cemizm/AnySensePro/Dokumentation/Anschluesse.png

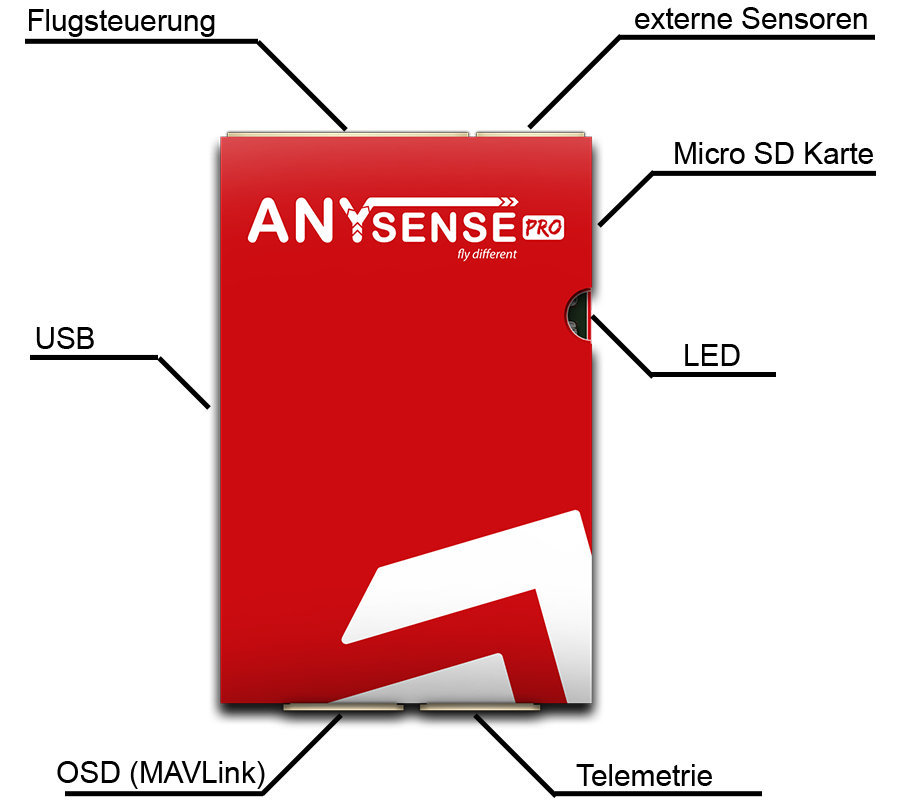
Dokumentation/Anschluesse.png
