cemizm/AnySensePro/Dokumentation/Aufkleber Be A Pro.png

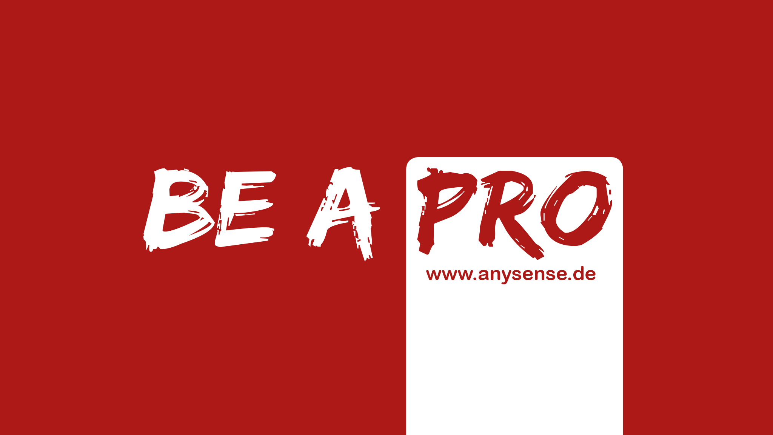
Dokumentation/Aufkleber Be A Pro.png
