cemizm/AnySensePro/Dokumentation/Fotos/AnySense Pro Detail 1.jpg

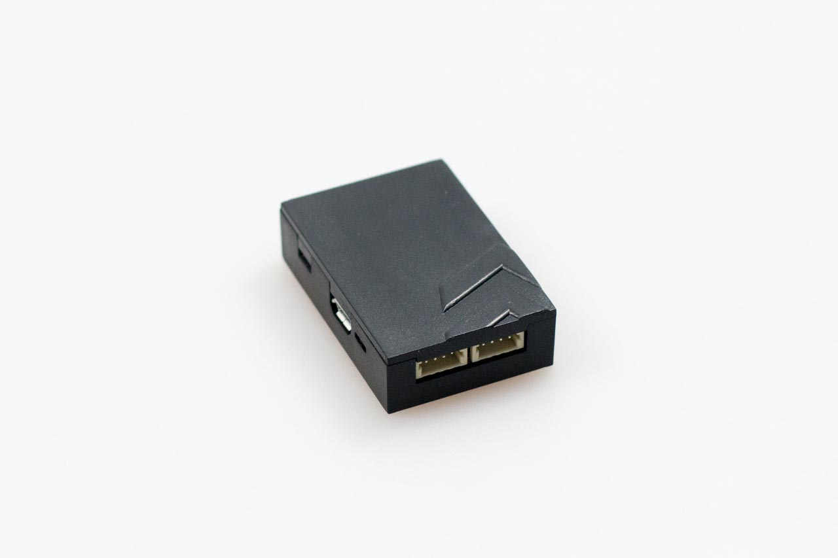
Dokumentation/Fotos/AnySense Pro Detail 1.jpg
