cemizm/AnySensePro/Dokumentation/Fotos/AnySense Pro Detail 2.jpg

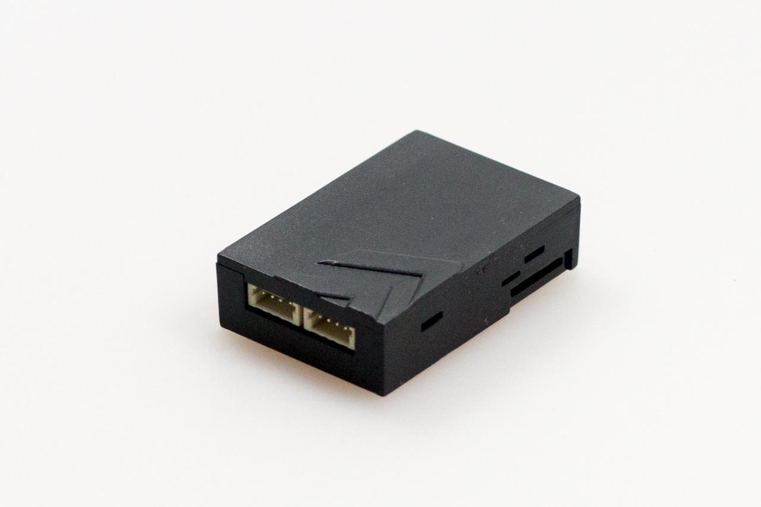
Dokumentation/Fotos/AnySense Pro Detail 2.jpg
