cemizm/AnySensePro/Dokumentation/Fotos/AnySense Pro Lieferumfang.jpg

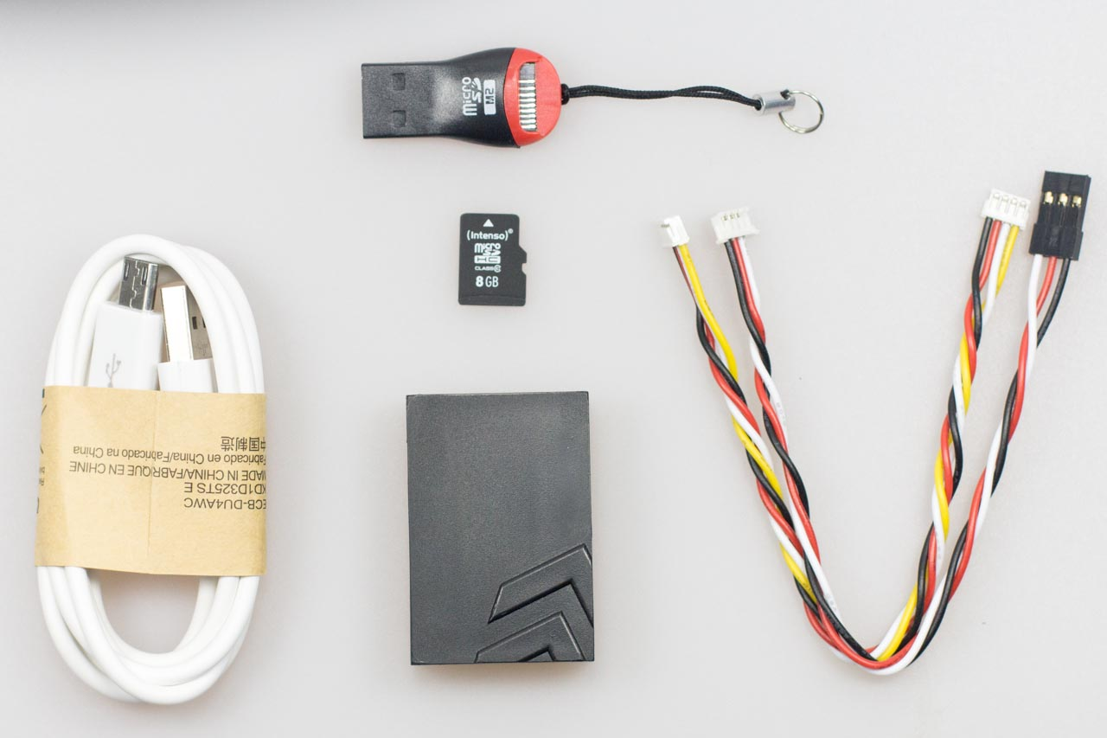
Dokumentation/Fotos/AnySense Pro Lieferumfang.jpg
