cemizm/AnySensePro/Dokumentation/Fotos/AnySense Pro Telemetrie Kabel.jpg

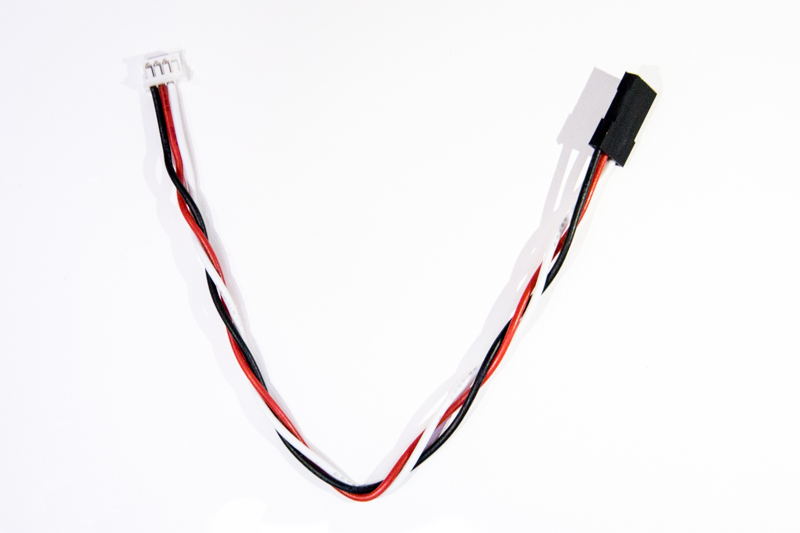
Dokumentation/Fotos/AnySense Pro Telemetrie Kabel.jpg
