cemizm/AnySensePro/Dokumentation/Fotos/AnySense Pro.jpg

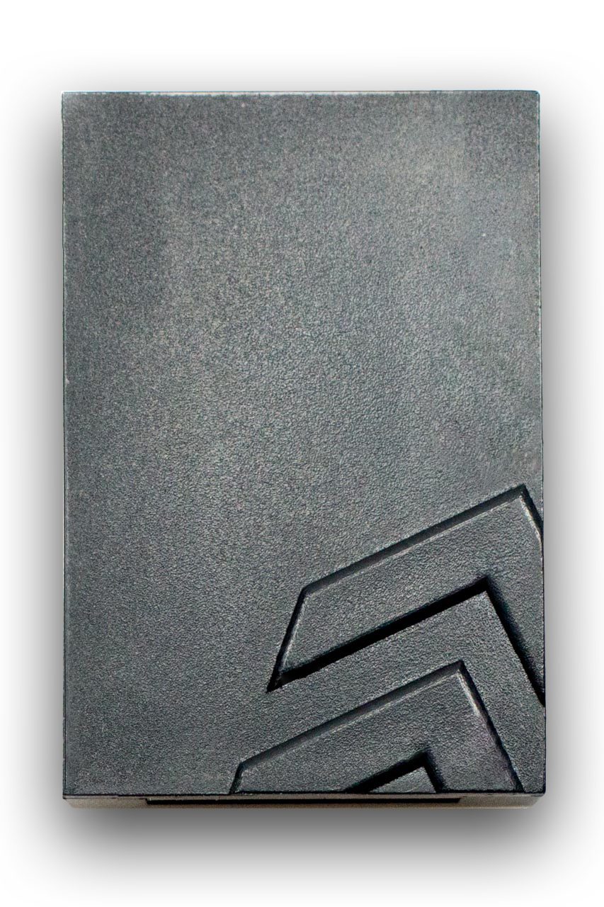
Dokumentation/Fotos/AnySense Pro.jpg
