cemizm/AnySensePro/Dokumentation/Fotos/AnySense Pro.png

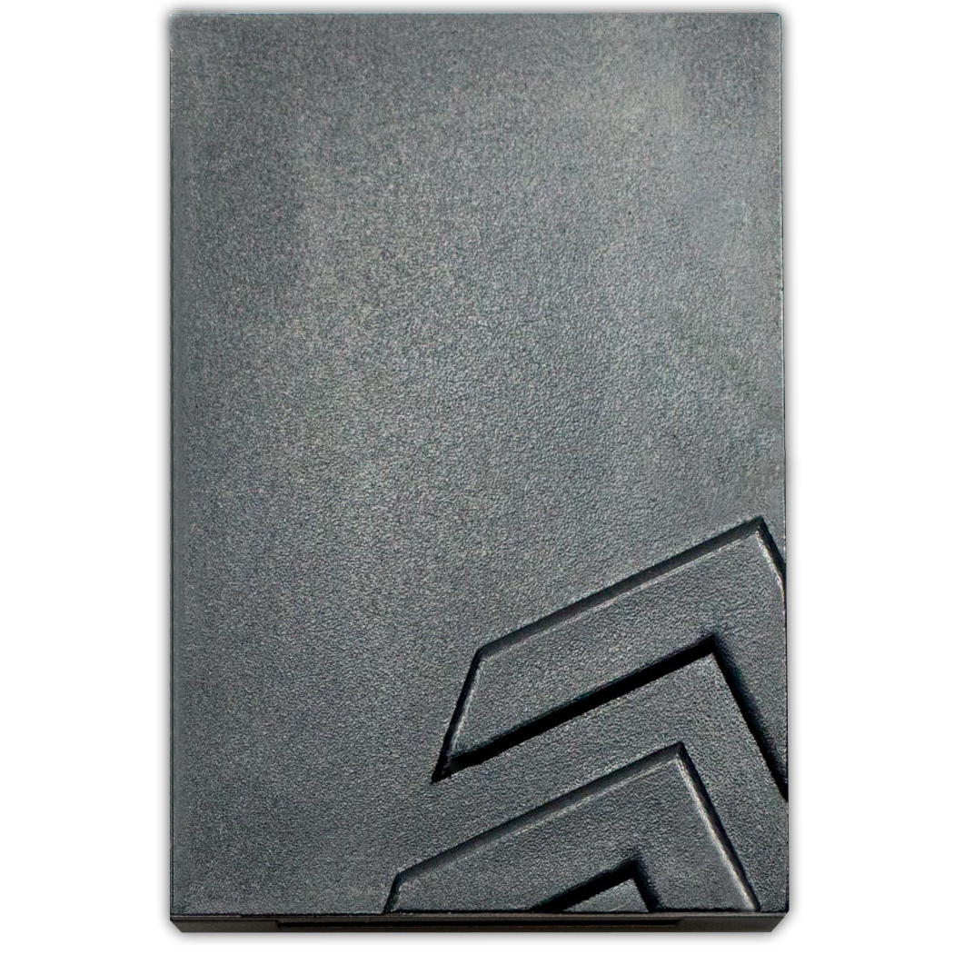
Dokumentation/Fotos/AnySense Pro.png
