cemizm/AnySensePro/Dokumentation/Fotos/Flugsteuerung Align.jpg

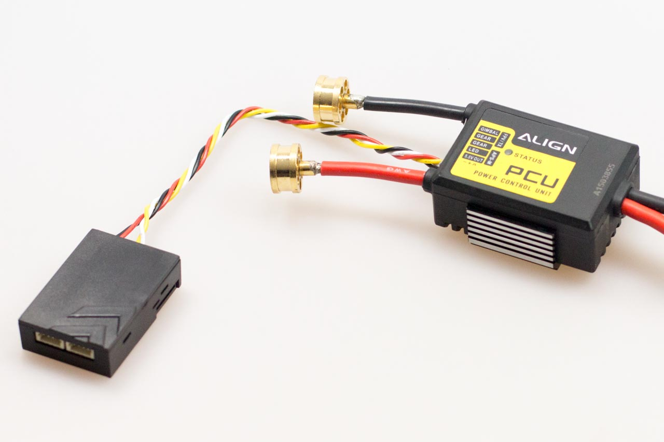
Dokumentation/Fotos/Flugsteuerung Align.jpg
