cemizm/AnySensePro/Dokumentation/Fotos/Flugsteuerung Naza.jpg

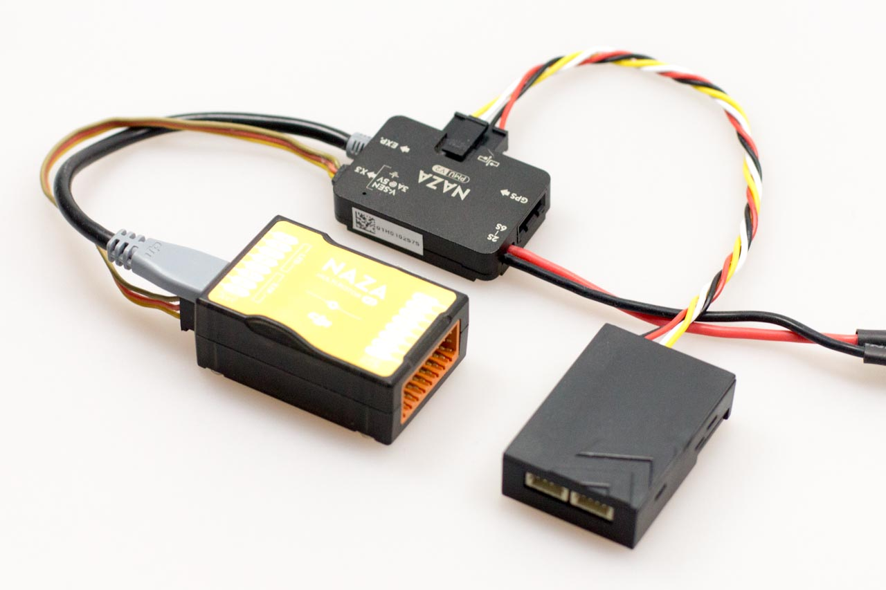
Dokumentation/Fotos/Flugsteuerung Naza.jpg
