cemizm/AnySensePro/Dokumentation/Fotos/Flugsteuerung Tarot.jpg

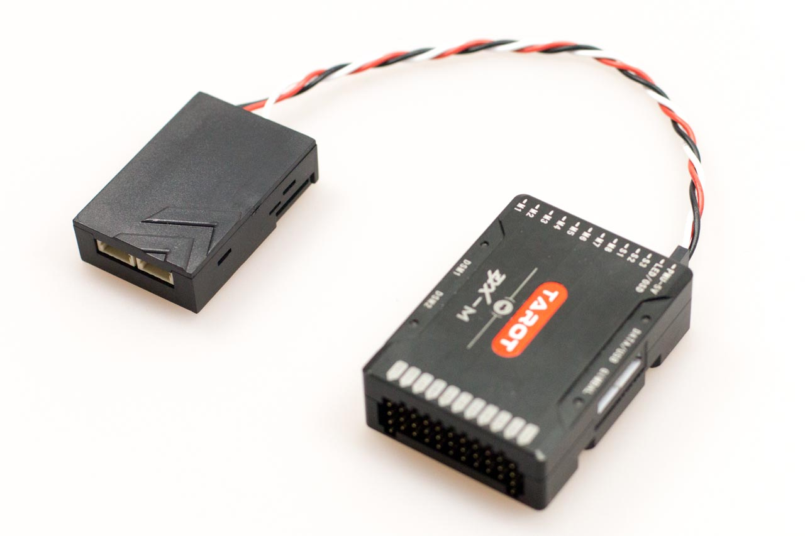
Dokumentation/Fotos/Flugsteuerung Tarot.jpg
