cemizm/AnySensePro/Dokumentation/Fotos/Kabel CANBus.jpg

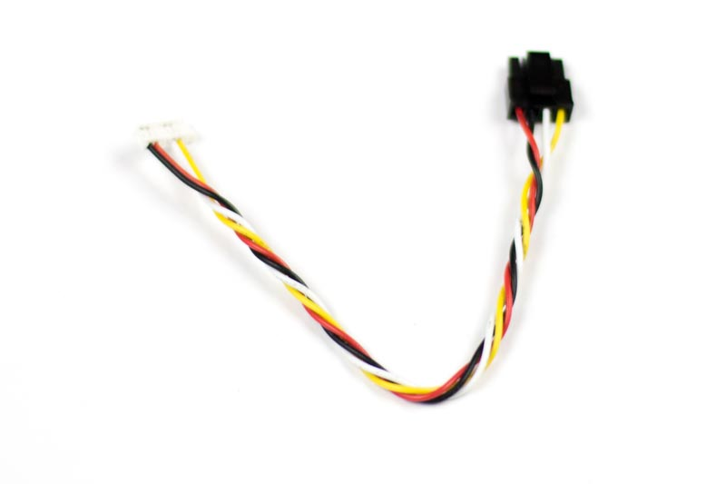
Dokumentation/Fotos/Kabel CANBus.jpg
