cemizm/AnySensePro/Dokumentation/Fotos/Kabel MAVLink.jpg

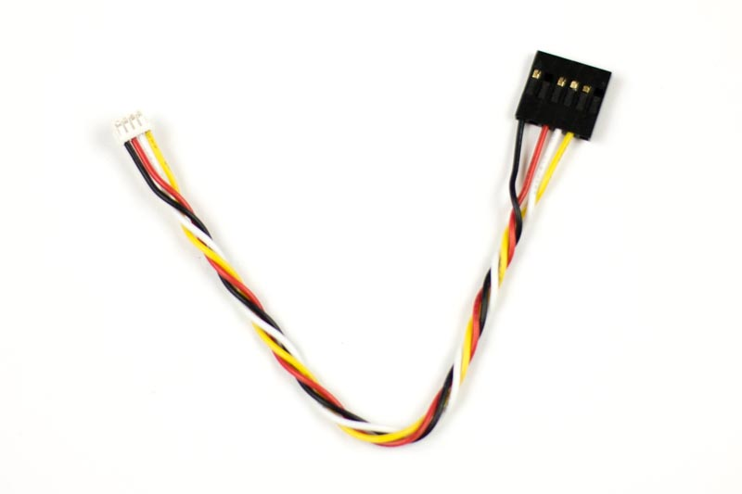
Dokumentation/Fotos/Kabel MAVLink.jpg
