cemizm/AnySensePro/Dokumentation/Fotos/Kabel PixHawk.jpg

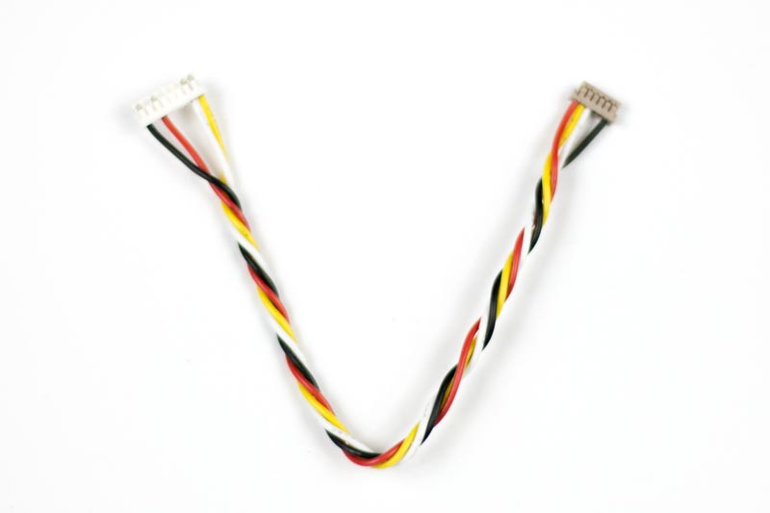
Dokumentation/Fotos/Kabel PixHawk.jpg
