cemizm/AnySensePro/Dokumentation/Fotos/Kabel Tarot.jpg

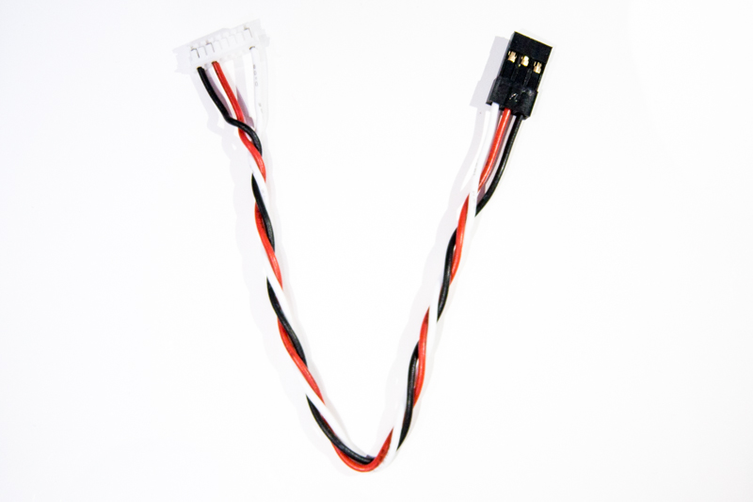
Dokumentation/Fotos/Kabel Tarot.jpg
