cemizm/AnySensePro/Dokumentation/Fotos/Telemetrie FrSky.jpg

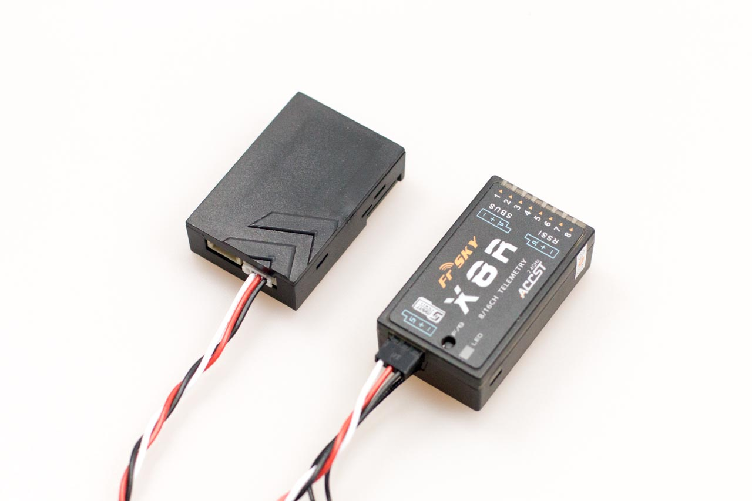
Dokumentation/Fotos/Telemetrie FrSky.jpg
