cemizm/AnySensePro/Dokumentation/Fotos/Telemetrie Futaba.jpg

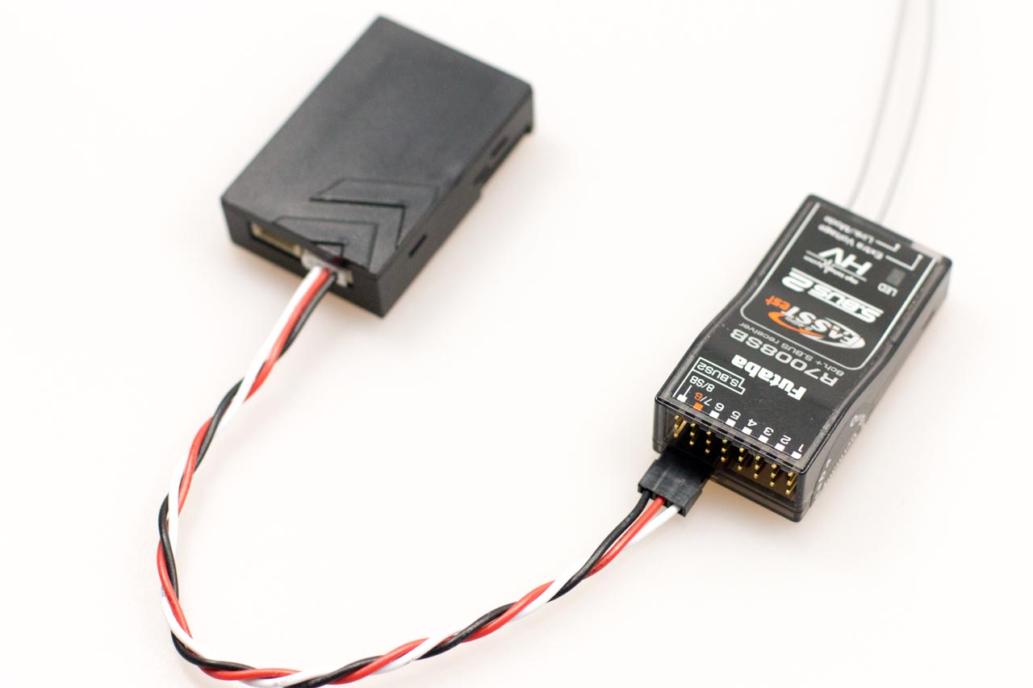
Dokumentation/Fotos/Telemetrie Futaba.jpg
