cemizm/AnySensePro/Dokumentation/Fotos/Telemetrie Graupner.jpg

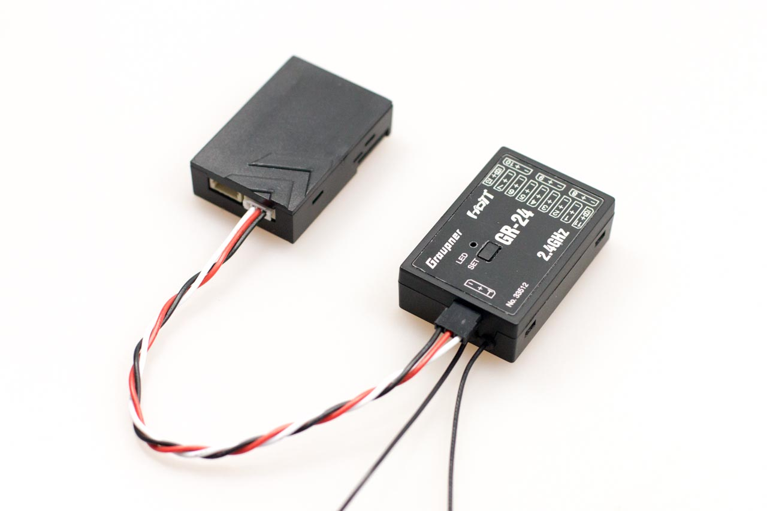
Dokumentation/Fotos/Telemetrie Graupner.jpg
