cemizm/AnySensePro/Dokumentation/Fotos/Telemetrie Jeti.jpg

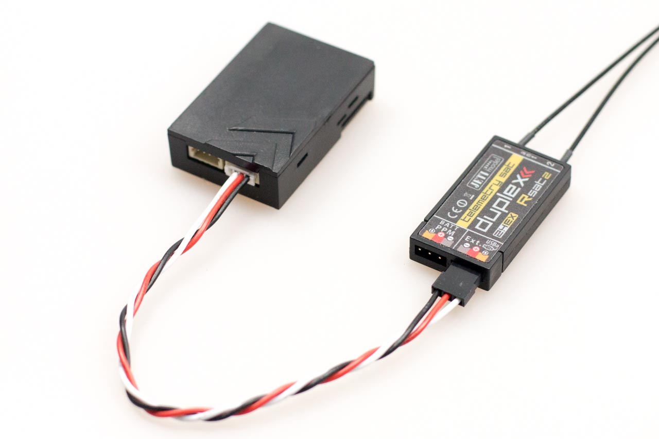
Dokumentation/Fotos/Telemetrie Jeti.jpg
