cemizm/AnySensePro/Dokumentation/Fotos/Telemetrie Multiplex.jpg

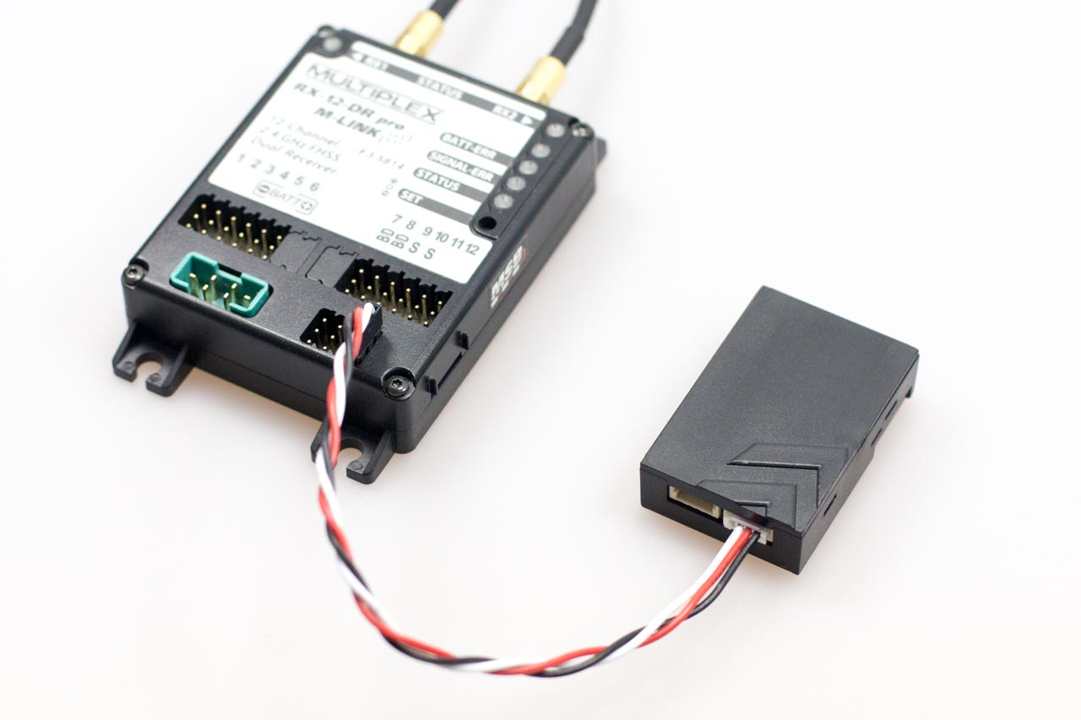
Dokumentation/Fotos/Telemetrie Multiplex.jpg
