cemizm/AnySensePro/Dokumentation/Fotos/Telemetrie Spektrum.jpg

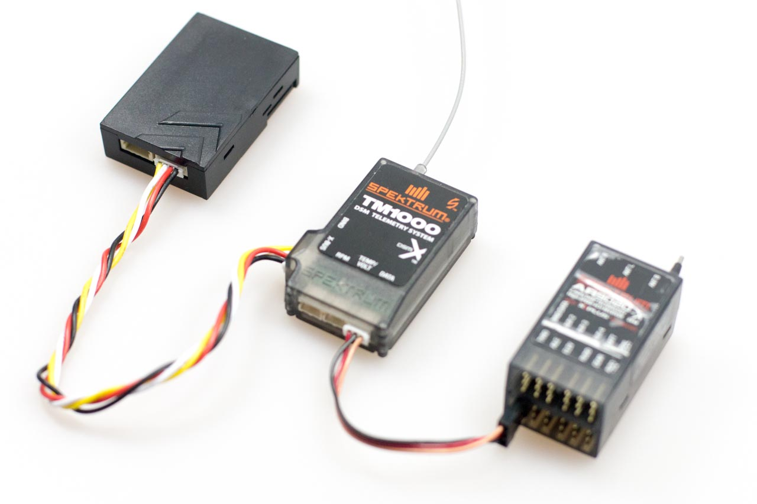
Dokumentation/Fotos/Telemetrie Spektrum.jpg
