cemizm/AnySensePro/Dokumentation/Futuba.JPG

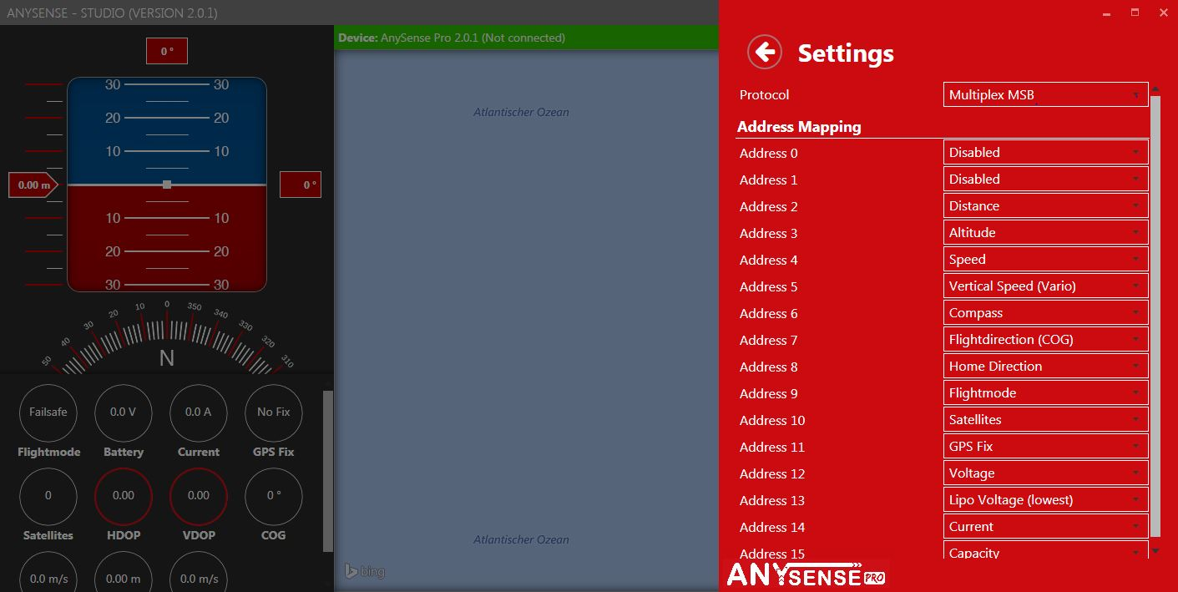
Dokumentation/Futuba.JPG
