cemizm/AnySensePro/Hardware/Kabel/CANBusKabel.pdf

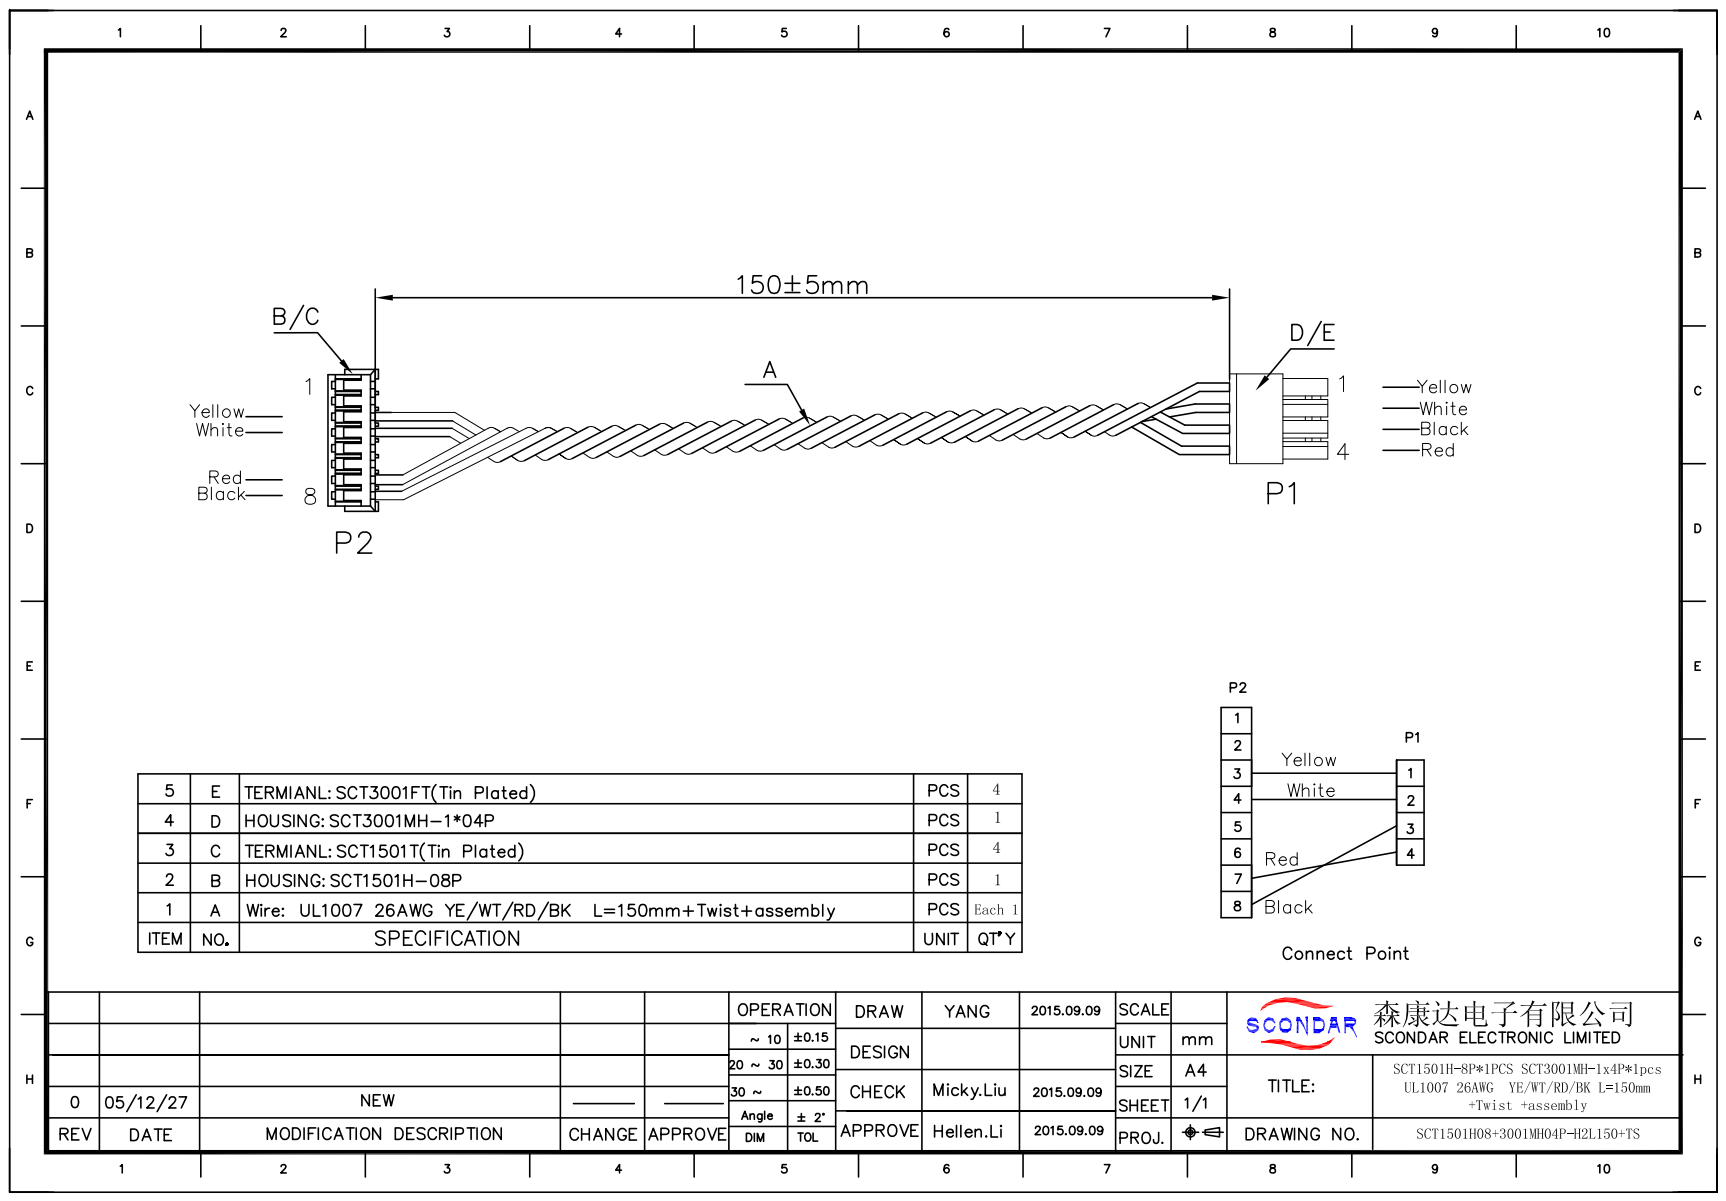
[picture p44: page 1]
