cemizm/AnySensePro/Hardware/Kabel/OSDKabel.pdf

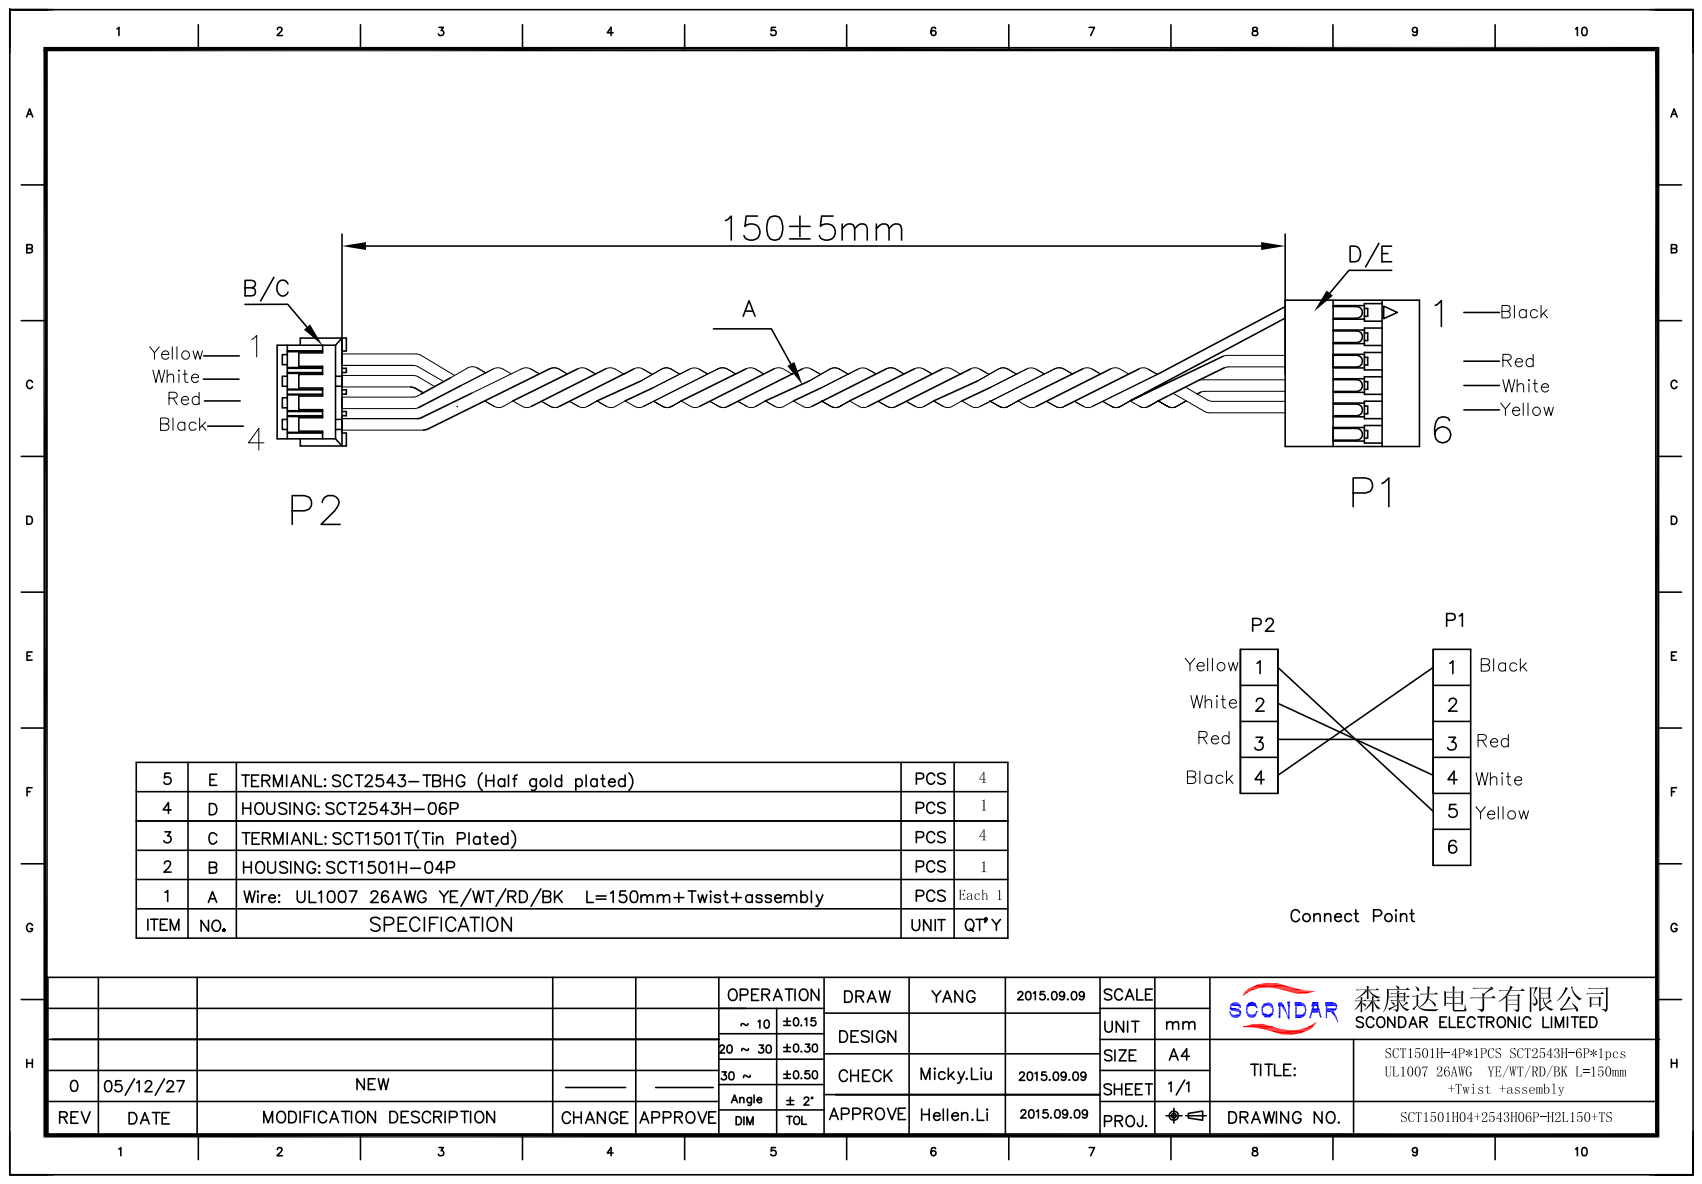
[picture p45: page 1]
