cemizm/AnySensePro/Hardware/Kabel/PixhawkKabel.pdf

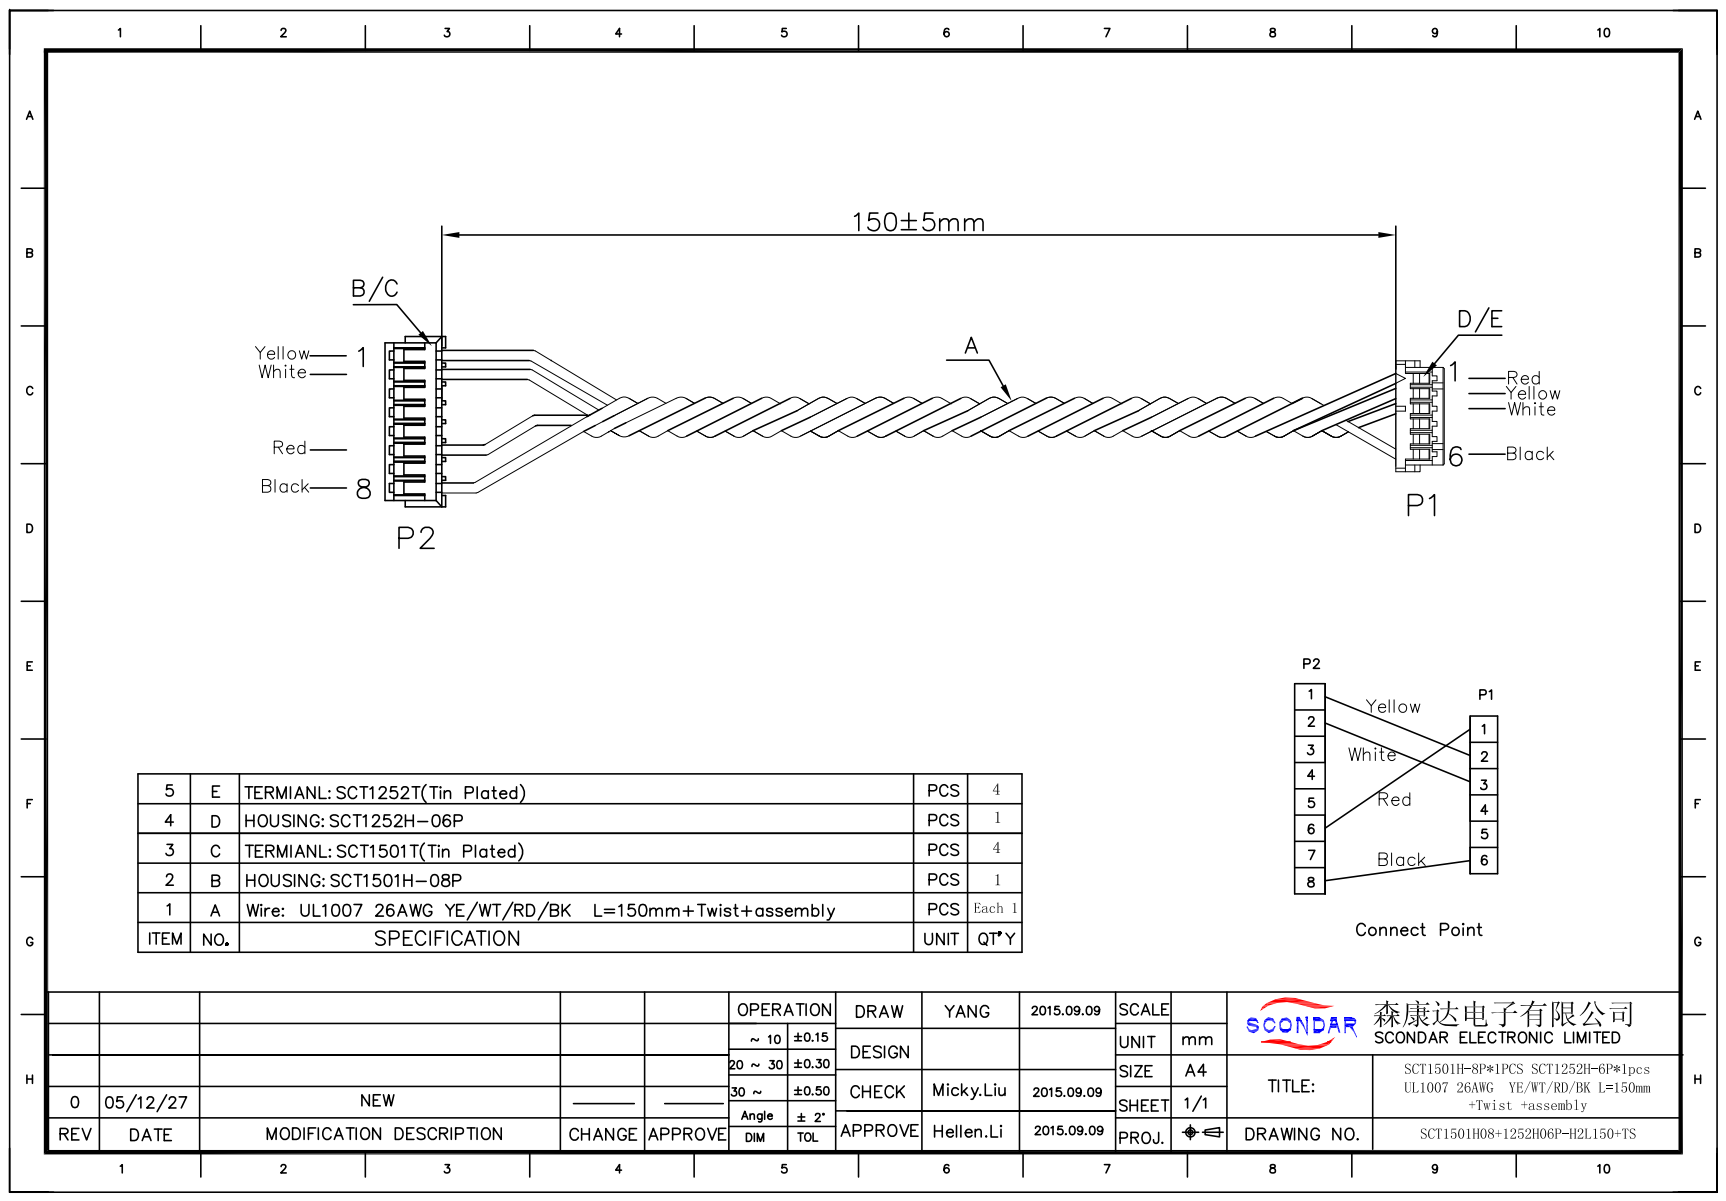
[picture p46: page 1]
