cemizm/AnySensePro/Hardware/Kabel/SpektrumKabel.pdf

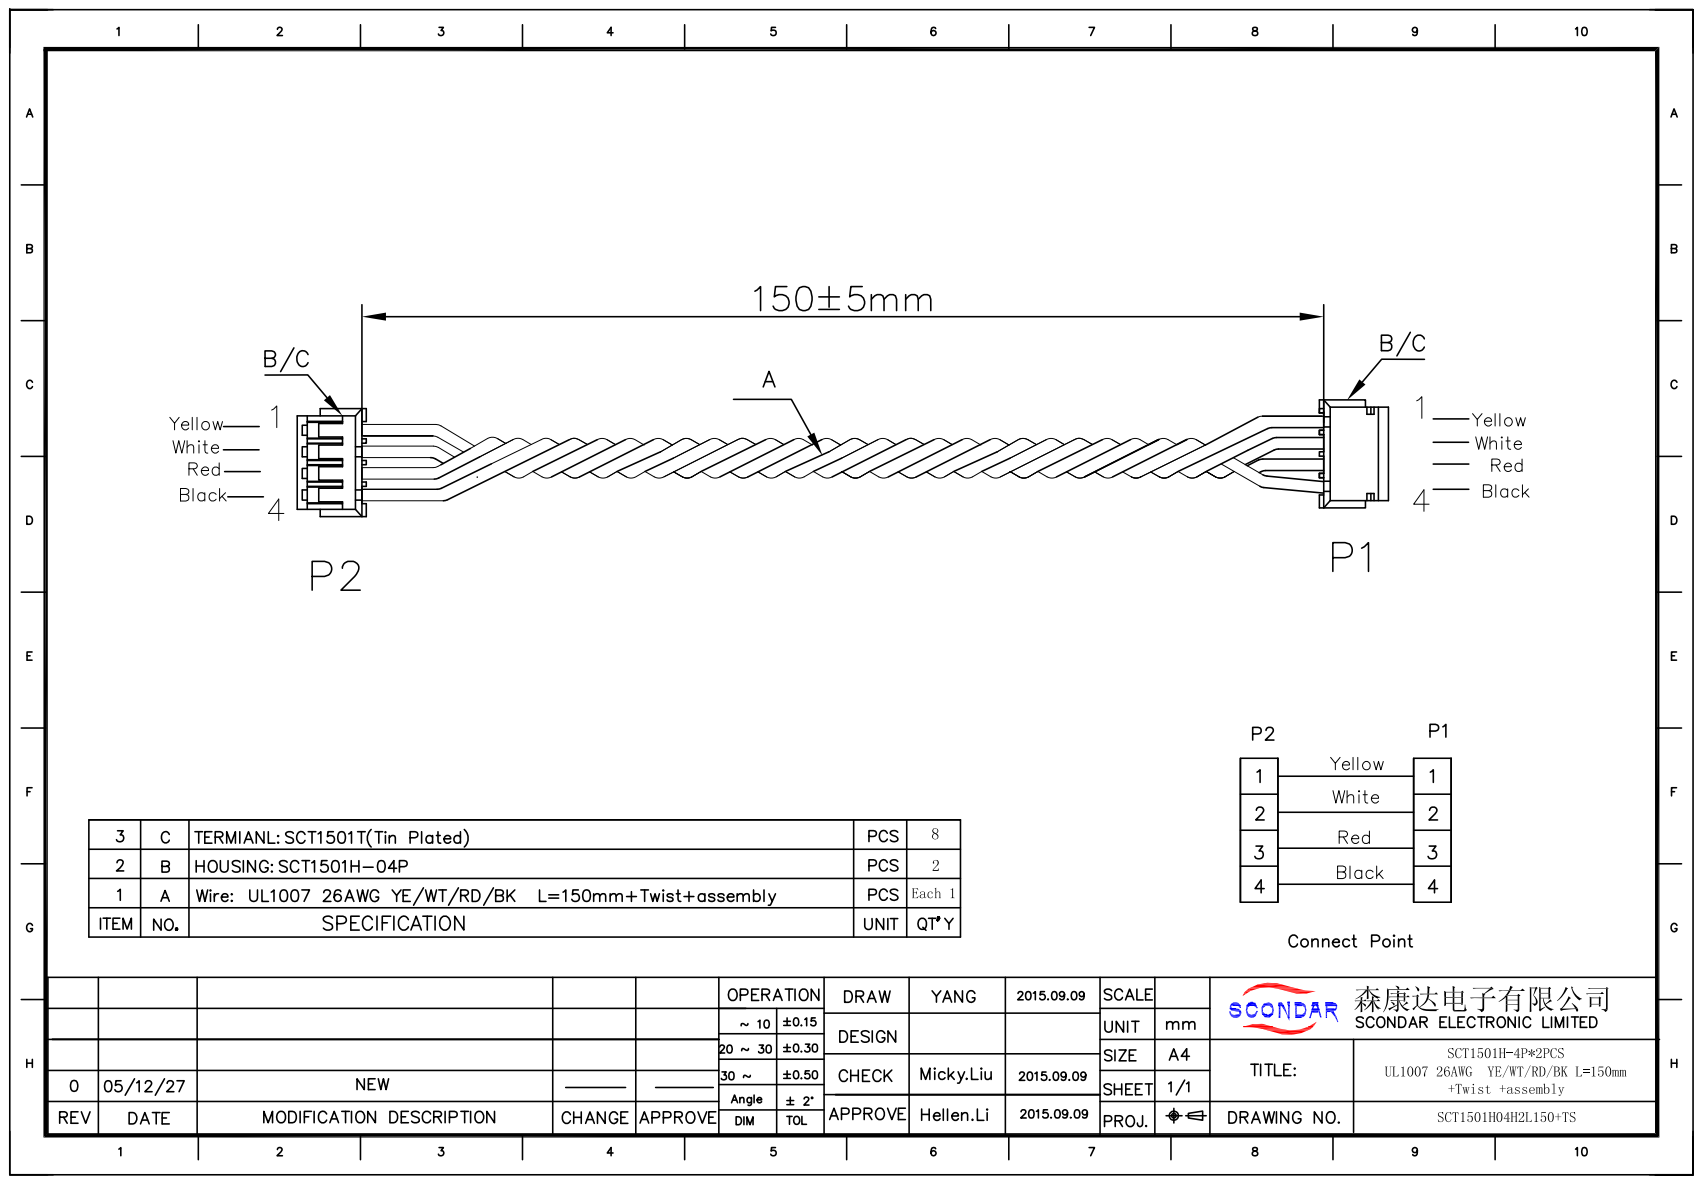
[picture p47: page 1]
