cemizm/AnySensePro/Hardware/Kabel/TelemetryKabel.pdf

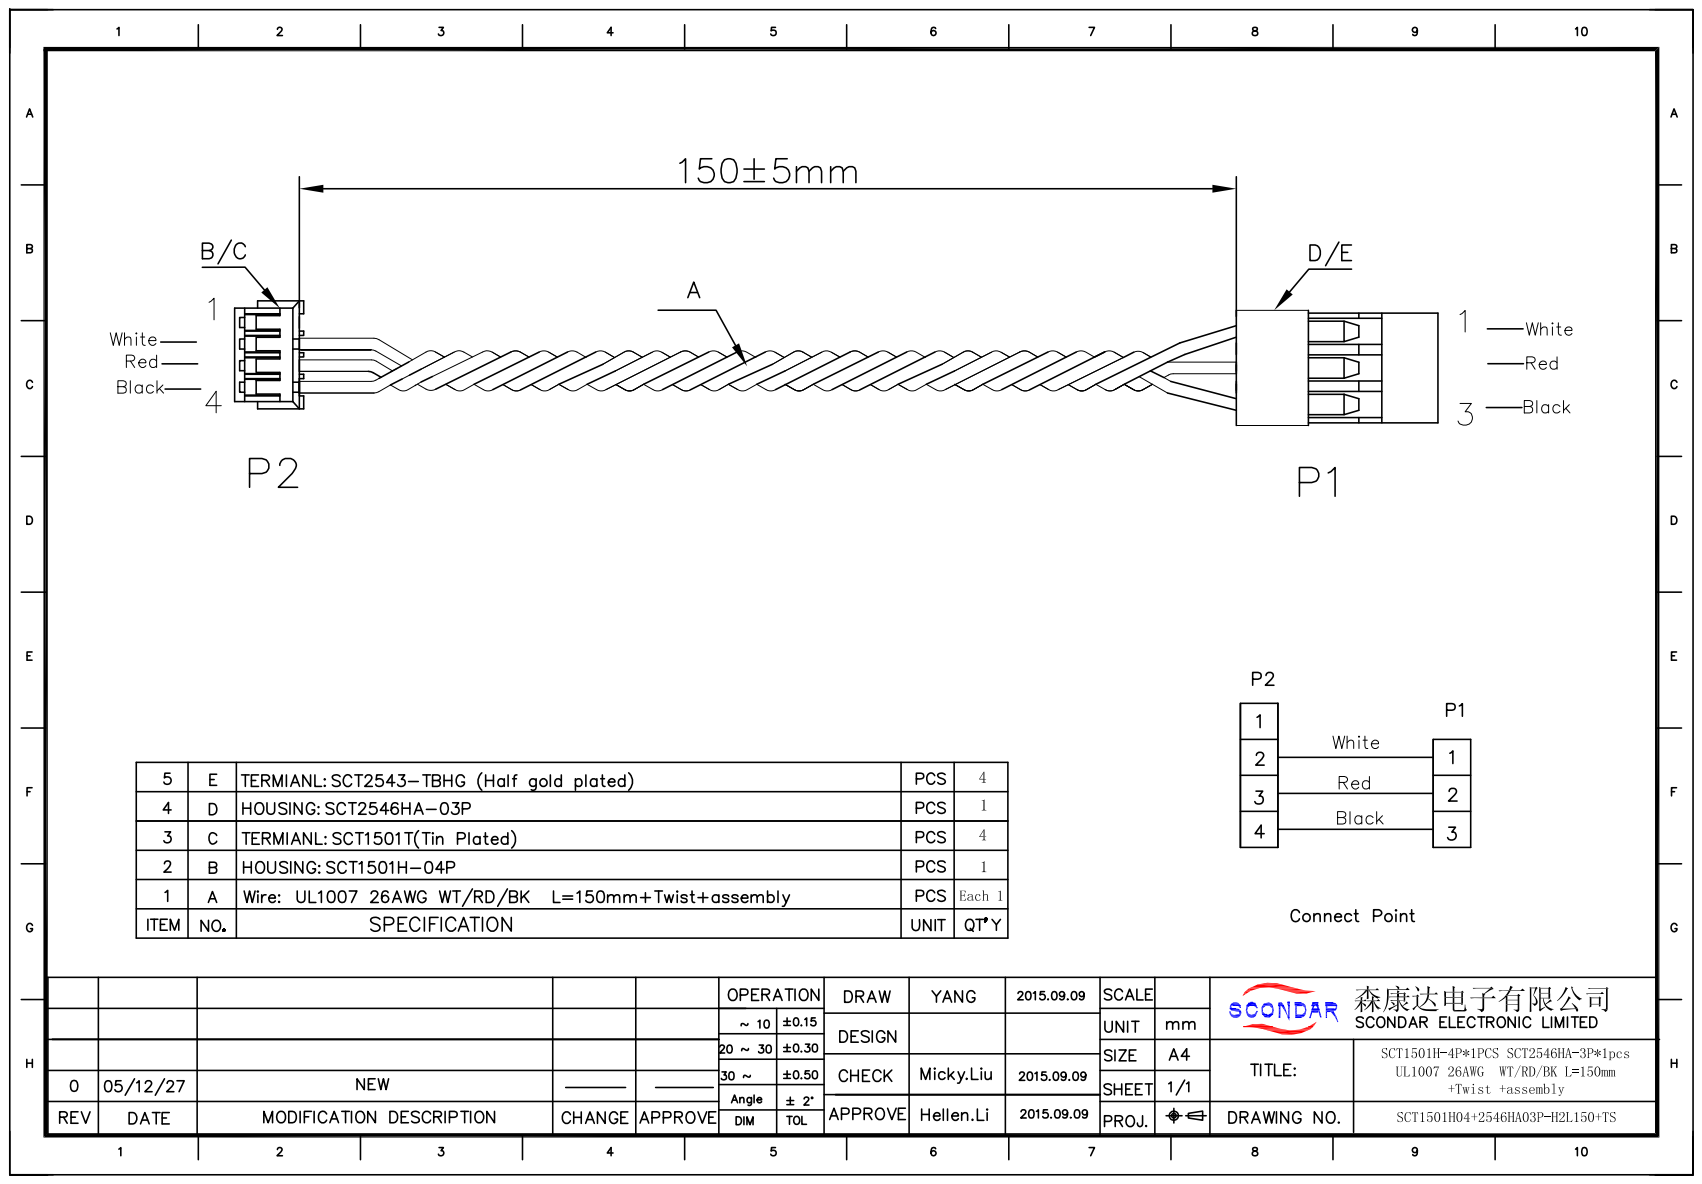
[picture p48: page 1]
