cemizm/AnySensePro/Firmware/shared/Application/source/Configuration.cpp

/*
 * Configuration.cpp
 *
 *  Created on: 15.10.2015
 *      Author: cem
 */

#include <Configuration.h>
#include <StorageFlashSPI.h>

namespace App
{

static_assert(offsetof(ConfigurationData, ProtocolSettings) == 32, "Protocol configuration will miss align!");

Configuration Config;

void Configuration::Init()
{
	if (Load() != 1)
		Save();

	if (LoadSystem() != 1)
		SaveSystem();

	if (m_data.Version < ConfigurationVersion)
	{
		for (uint8_t i = m_data.Version + 1; i <= ConfigurationVersion; i++)
		{
			if(i == 1) // Update to Config Version 1
			{
				m_data.AlarmDistance = 2000;
				m_data.AlarmVoltage = 15;
			}
		}

		Save();
	}
}

uint8_t Configuration::Load()
{
	return LoadFile(&m_data, sizeof(ConfigurationData), cfgname);
}

uint8_t Configuration::Save()
{
	m_data.Version = ConfigurationVersion;
	return SaveFile(&m_data, sizeof(ConfigurationData), cfgname);
}

uint8_t Configuration::LoadFile(void* data, uint16_t size, const char* file)
{
	spiffs_file fd = Storage::StorageFlashSPI::Open(file, SPIFFS_RDONLY, 0);

	if (fd < 0)
		return 0;

	Storage::StorageFlashSPI::FileAutoRelease far(fd);

	spiffs_stat st;

	if (Storage::StorageFlashSPI::FileStat(fd, &st) < 0)
		return 0;

	if (st.size == 0)
	{
		far.Release();
		Storage::StorageFlashSPI::Remove(file);
		return 0;
	}

	if (Storage::StorageFlashSPI::Read(fd, data, size) < 0)
		return 0;

	return 1;
}

uint8_t Configuration::SaveFile(void* data, uint16_t size, const char* file)
{
	spiffs_file fd = Storage::StorageFlashSPI::Open(file, SPIFFS_CREAT | SPIFFS_TRUNC | SPIFFS_RDWR, 0);
	if (fd < 0)
		return 0;

	if (Storage::StorageFlashSPI::Write(fd, data, (uint32_t) size) < 0)
		return 0;

	if (Storage::StorageFlashSPI::Close(fd) < 0)
		return 0;

	return 1;

}

uint8_t Configuration::LoadSystem()
{
	return LoadFile(&m_SystemData, sizeof(SystemData), intname);
}
uint8_t Configuration::SaveSystem()
{
	return SaveFile(&m_SystemData, sizeof(SystemData), intname);
}

void Configuration::AddUpdateHandler(ConfigurationChanged& handler)
{
	for (uint8_t i = 0; i < MaxHandlers; i++)
	{
		if (m_handlers[i] == nullptr)
		{
			m_handlers[i] = &handler;
			return;
		}
	}
}

void Configuration::RemoveUpdateHandler(ConfigurationChanged& handler)
{
	for (uint8_t i = 0; i < MaxHandlers; i++)
	{
		if (m_handlers[i] == &handler)
		{
			m_handlers[i] = nullptr;
			return;
		}
	}
}

void Configuration::NotifyHandler()
{
	for (uint8_t i = 0; i < MaxHandlers; i++)
	{
		if (m_handlers[i] != nullptr)
			m_handlers[i]->UpdateConfiguration();
	}
}

ConfigurationData& Configuration::GetConfiguration()
{
	return m_data;
}

void Configuration::SetConfiguration(ConfigurationData& data)
{
	memcpy(&m_data, &data, sizeof(ConfigurationData));
	Save();
	NotifyHandler();
}

uint8_t Configuration::GetVersion()
{
	return m_data.Version;
}

void Configuration::SetVersion(uint8_t version)
{
	if (m_data.Version == version)
		return;

	m_data.Version = version;
	Save();
}

TelemetryProtocol Configuration::GetProtocol()
{
	return m_data.Protocol;
}

void Configuration::SetProtocol(TelemetryProtocol protocol)
{
	if (m_data.Protocol == protocol)
		return;

	m_data.Protocol = protocol;
	Save();
}

uint32_t Configuration::GetNextFlightNumber()
{
	return m_SystemData.FlightNumber;
}

void Configuration::UpdateFlightNumber()
{
	m_SystemData.FlightNumber++;
	SaveSystem();
}

} /* namespace Application */
